hackdaworld/gmote/firmware/mynewt/hw/bsp/gmote/include/bsp/bsp.h

/**
 * Licensed to the Apache Software Foundation (ASF) under one
 * or more contributor license agreements.  See the NOTICE file
 * distributed with this work for additional information
 * regarding copyright ownership.  The ASF licenses this file
 * to you under the Apache License, Version 2.0 (the
 * "License"); you may not use this file except in compliance
 * with the License.  You may obtain a copy of the License at
 *
 *  http://www.apache.org/licenses/LICENSE-2.0
 *
 * Unless required by applicable law or agreed to in writing,
 * software distributed under the License is distributed on an
 * "AS IS" BASIS, WITHOUT WARRANTIES OR CONDITIONS OF ANY
 * KIND, either express or implied.  See the License for the
 * specific language governing permissions and limitations
 * under the License.
 */
#ifndef H_BSP_H
#define H_BSP_H

#include <inttypes.h>
#include <mcu/mcu.h>
#include "os/mynewt.h"

#ifdef __cplusplus
extern "C" {
#endif

/* Define special stackos sections */
#define sec_data_core   __attribute__((section(".data.core")))
#define sec_bss_core    __attribute__((section(".bss.core")))
#define sec_bss_nz_core __attribute__((section(".bss.core.nz")))

/* More convenient section placement macros. */
#define bssnz_t         sec_bss_nz_core

/*
 * Symbols from linker script.
 */
extern uint8_t _ram_start;
#define RAM_SIZE (8 *1024)

/* LED pins */
#define LED_BLINK_PIN MCU_GPIO_PORTA(3)
   
/* SX1276 pins / SPI defined in syscfg.yml */
// PA14 used as not connected!
#define MCU_GPIO_NC		MCU_GPIO_PORTA(14)
#define SX1276_DIO0		MCU_GPIO_PORTA(13)
#define SX1276_DIO1		MCU_GPIO_PORTA(12)
#define SX1276_DIO2		MCU_GPIO_NC
#define SX1276_DIO3		MCU_GPIO_NC
#define SX1276_DIO4		MCU_GPIO_NC
#define SX1276_DIO5		MCU_GPIO_NC
#define SX1276_NRESET		MCU_GPIO_PORTA(11)
#define SX1276_RXTX		MCU_GPIO_NC
#define SX1276_ANT_HF_CTRL	MCU_GPIO_NC

/* Arduino pins */
#define ARDUINO_PIN_D0      MCU_GPIO_PORTA(3)
#define ARDUINO_PIN_D1      MCU_GPIO_PORTA(2)
#define ARDUINO_PIN_D2      MCU_GPIO_PORTA(10)
#define ARDUINO_PIN_D3      MCU_GPIO_PORTB(3)
#define ARDUINO_PIN_D4      MCU_GPIO_PORTB(5)
#define ARDUINO_PIN_D5      MCU_GPIO_PORTB(4)
#define ARDUINO_PIN_D6      MCU_GPIO_PORTB(10)
#define ARDUINO_PIN_D7      MCU_GPIO_PORTA(8)
#define ARDUINO_PIN_D8      MCU_GPIO_PORTA(9)
#define ARDUINO_PIN_D9      MCU_GPIO_PORTC(7)
#define ARDUINO_PIN_D10     MCU_GPIO_PORTB(6)
#define ARDUINO_PIN_D11     MCU_GPIO_PORTA(7)
#define ARDUINO_PIN_D12     MCU_GPIO_PORTA(6)
#define ARDUINO_PIN_D13     MCU_GPIO_PORTA(5)
#define ARDUINO_PIN_A0      MCU_GPIO_PORTA(0)
#define ARDUINO_PIN_A1      MCU_GPIO_PORTA(1)
#define ARDUINO_PIN_A2      MCU_GPIO_PORTA(4)
#define ARDUINO_PIN_A3      MCU_GPIO_PORTB(0)
#define ARDUINO_PIN_A4      MCU_GPIO_PORTC(1)
#define ARDUINO_PIN_A5      MCU_GPIO_PORTC(0)

#define ARDUINO_PIN_RX      ARDUINO_PIN_D0
#define ARDUINO_PIN_TX      ARDUINO_PIN_D1

#define ARDUINO_PIN_SCL     MCU_GPIO_PORTB(8)
#define ARDUINO_PIN_SDA     MCU_GPIO_PORTB(9)

#define ARDUINO_PIN_SCK     ARDUINO_PIN_D13
#define ARDUINO_PIN_MOSI    ARDUINO_PIN_D11
#define ARDUINO_PIN_MISO    ARDUINO_PIN_D12

#ifdef __cplusplus
}
#endif

#endif  /* H_BSP_H */
